Badbird5907/deltaboard/PCB/Components/stabalizers/Stabilizer_MX_6.00u.step

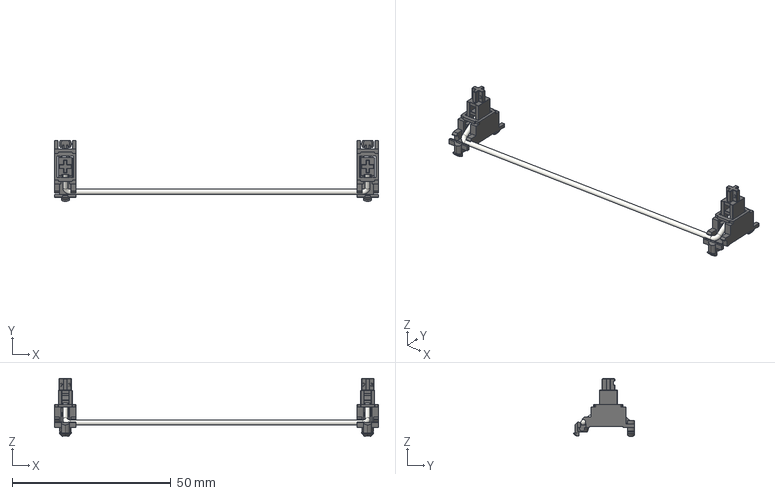
[picture p22: CAD file, 2025-03-12]
PCB/Components/stabalizers/Stabilizer_MX_6.00u.step
102.1 x 19.2 x 18.3 mm
